galacticstudios/Logic-Meter/firmware/src/usbcdc.h

/*******************************************************************************
  MPLAB Harmony Application Header File

  Company:
    Microchip Technology Inc.

  File Name:
    usbcdc.h

  Summary:
    This header file provides prototypes and definitions for the application.

  Description:
    This header file provides function prototypes and data type definitions for
    the application.  Some of these are required by the system (such as the
    "USBCDC_Initialize" and "USBCDC_Tasks" prototypes) and some of them are only used
    internally by the application (such as the "USBCDC_STATES" definition).  Both
    are defined here for convenience.
*******************************************************************************/

#ifndef _USBCDC_H
#define _USBCDC_H

// *****************************************************************************
// *****************************************************************************
// Section: Included Files
// *****************************************************************************
// *****************************************************************************

#include <stdint.h>
#include <stdbool.h>
#include <stddef.h>
#include <stdlib.h>
#include "configuration.h"
#include "definitions.h"

// DOM-IGNORE-BEGIN
#ifdef __cplusplus  // Provide C++ Compatibility

extern "C" {

#endif
// DOM-IGNORE-END

// *****************************************************************************
// *****************************************************************************
// Section: Type Definitions
// *****************************************************************************
// *****************************************************************************
#define USBCDC_READ_BUFFER_SIZE                                512

// *****************************************************************************
/* Application states

  Summary:
    Application states enumeration

  Description:
    This enumeration defines the valid application states.  These states
    determine the behavior of the application at various times.
*/

typedef enum
{
    /* Application's state machine's initial state. */
    USBCDC_STATE_INIT=0,

    /* Application waits for device configuration*/
    USBCDC_STATE_WAIT_FOR_CONFIGURATION,
            
    USBCDC_STATE_RUNNING,

    /* Wait for a character receive */
    USBCDC_STATE_SCHEDULE_READ,

    /* A character is received from host */
    USBCDC_STATE_WAIT_FOR_READ_COMPLETE,

    /* Wait for the TX to get completed */
    USBCDC_STATE_SCHEDULE_WRITE,

    /* Wait for the write to complete */
    USBCDC_STATE_WAIT_FOR_WRITE_COMPLETE,

    /* Application Error state*/
    USBCDC_STATE_ERROR

} USBCDC_STATES;


// *****************************************************************************
/* Application Data

  Summary:
    Holds application data

  Description:
    This structure holds the application's data.

  Remarks:
    Application strings and buffers are be defined outside this structure.
 */

typedef struct
{
    /* Device layer handle returned by device layer open function */
    USB_DEVICE_HANDLE deviceHandle;

    /* Application's current state*/
    USBCDC_STATES state;

    /* Set Line Coding Data */
    USB_CDC_LINE_CODING setLineCodingData;

    /* Device configured state */
    bool isConfigured;

    /* Get Line Coding Data */
    USB_CDC_LINE_CODING getLineCodingData;

    /* Control Line State */
    USB_CDC_CONTROL_LINE_STATE controlLineStateData;

    /* Read transfer handle */
    USB_DEVICE_CDC_TRANSFER_HANDLE readTransferHandle;

    /* Write transfer handle */
    USB_DEVICE_CDC_TRANSFER_HANDLE writeTransferHandle;

    /* True if a character was read */
    bool isReadComplete;

    /* True if a character was written*/
    bool isWriteComplete;

    /* Flag determines SOF event occurrence */
    bool sofEventHasOccurred;

    /* Break data */
    uint16_t breakData;

    /* Application CDC read buffer */
    uint8_t * cdcReadBuffer;

    /* Application CDC Write buffer */
    uint8_t * cdcWriteBuffer;

    /* Number of bytes read from Host */ 
    uint32_t numBytesRead; 
} USBCDC_DATA;

// *****************************************************************************
// *****************************************************************************
// Section: Application Callback Routines
// *****************************************************************************
// *****************************************************************************
/* These routines are called by drivers when certain events occur.
*/

// *****************************************************************************
// *****************************************************************************
// Section: Application Initialization and State Machine Functions
// *****************************************************************************
// *****************************************************************************

/*******************************************************************************
  Function:
    void USBCDC_Initialize ( void )

  Summary:
     MPLAB Harmony application initialization routine.

  Description:
    This function initializes the Harmony application.  It places the
    application in its initial state and prepares it to run so that its
    USBCDC_Tasks function can be called.

  Precondition:
    All other system initialization routines should be called before calling
    this routine (in "SYS_Initialize").

  Parameters:
    None.

  Returns:
    None.

  Example:
    <code>
    USBCDC_Initialize();
    </code>

  Remarks:
    This routine must be called from the SYS_Initialize function.
*/

void USBCDC_Initialize ( void );


/*******************************************************************************
  Function:
    void USBCDC_Tasks ( void )

  Summary:
    MPLAB Harmony Demo application tasks function

  Description:
    This routine is the Harmony Demo application's tasks function.  It
    defines the application's state machine and core logic.

  Precondition:
    The system and application initialization ("SYS_Initialize") should be
    called before calling this.

  Parameters:
    None.

  Returns:
    None.

  Example:
    <code>
    USBCDC_Tasks();
    </code>

  Remarks:
    This routine must be called from SYS_Tasks() routine.
 */

void USBCDC_Tasks( void );



#endif /* _USBCDC_H */

//DOM-IGNORE-BEGIN
#ifdef __cplusplus
}
#endif
//DOM-IGNORE-END

/*******************************************************************************
 End of File
 */
