galacticstudios/Logic-Meter/firmware/src/Interrupts.cpp

/* 
 * File:   Interrupts.cpp
 * Author: Bob
 * 
 * Created on September 14, 2020, 9:30 AM
 */

extern "C"
{
#include "definitions.h"
}
#include "Interrupts.h"

const SPIIntMeta SPIInt[] = 
{
#if defined(__32MZ2048EFH064__)
    // SPI1
    {
        // Fault
        IntMeta(_SPI1_FAULT_VECTOR),
        // Receive Done
        IntMeta(_SPI1_RX_VECTOR),
        // Transfer Done
        IntMeta(_SPI1_TX_VECTOR),
    },
    // SPI2
    {
        // Fault
        IntMeta(_SPI2_FAULT_VECTOR),
        // Receive Done
        IntMeta(_SPI2_RX_VECTOR),
        // Transfer Done
        IntMeta(_SPI2_TX_VECTOR),
    },
    // SPI3
    {
        // Fault
        IntMeta(_SPI3_FAULT_VECTOR),
        // Receive Done
        IntMeta(_SPI3_RX_VECTOR),
        // Transfer Done
        IntMeta(_SPI3_TX_VECTOR),
    },
    // SPI4
    {
        // Fault
        IntMeta(_SPI4_FAULT_VECTOR),
        // Receive Done
        IntMeta(_SPI4_RX_VECTOR),
        // Transfer Done
        IntMeta(_SPI4_TX_VECTOR),
    },
    
#else
#error No SPI Interrupt metadata defined for this microcontroller
#endif
};

const UARTIntMeta UARTInt[] = 
{
#if defined(__32MZ2048EFH064__)
    // UART1
    {
        // Fault
        IntMeta(_UART1_FAULT_VECTOR),
        // Receive Done
        IntMeta(_UART1_RX_VECTOR),
        // Transfer Done
        IntMeta(_UART1_TX_VECTOR),
    },
    // UART2
    {
        // Fault
        IntMeta(_UART2_FAULT_VECTOR),
        // Receive Done
        IntMeta(_UART2_RX_VECTOR),
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
    {
        IntMeta(_DMA5_VECTOR),
    },
    // DMA6
    {
        IntMeta(_DMA6_VECTOR),
    },
    // DMA7
    {
        IntMeta(_DMA7_VECTOR),
    },
    
#else
#error No DMA Interrupt metadata defined for this microcontroller
#endif
};

UserInterruptHandler userInterruptHandlers[213];
